OE9SAU/Digitale-Loetstation/pics/Comp2.png

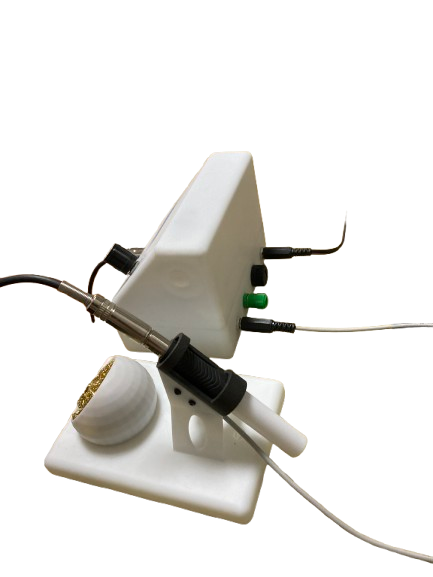
pics/Comp2.png
