OE9SAU/Digitale-Loetstation/pics/Encoder-wiring.jpg

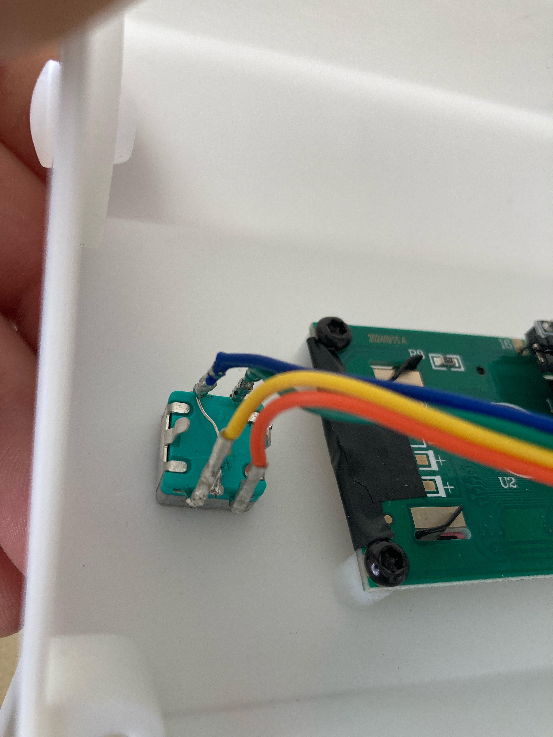
pics/Encoder-wiring.jpg
